yury-g/usb-buddy/docs/images/01-cable-pair.jpg

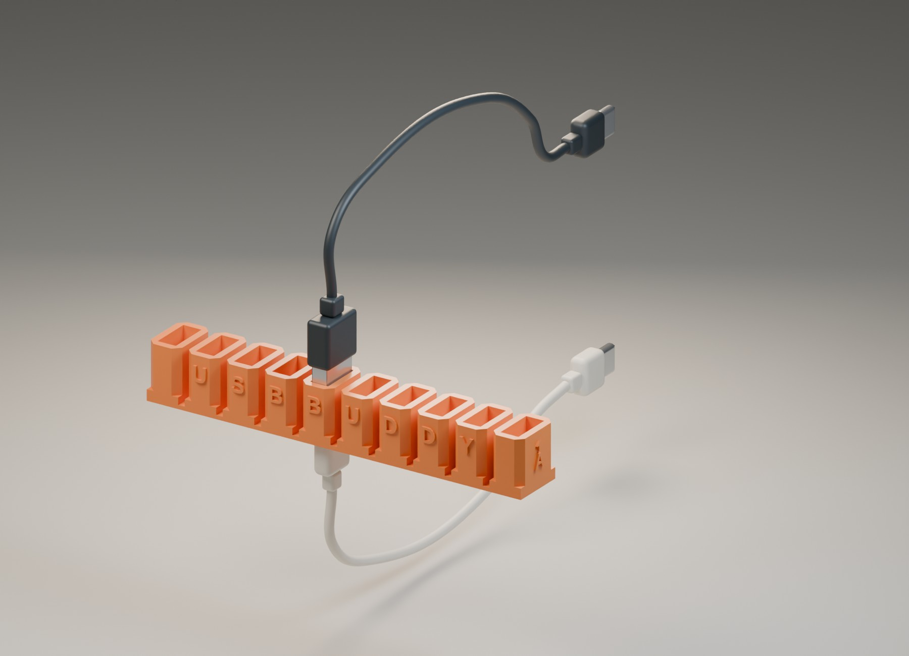
docs/images/01-cable-pair.jpg
