yury-g/usb-buddy/docs/images/drawer-before-after.jpg

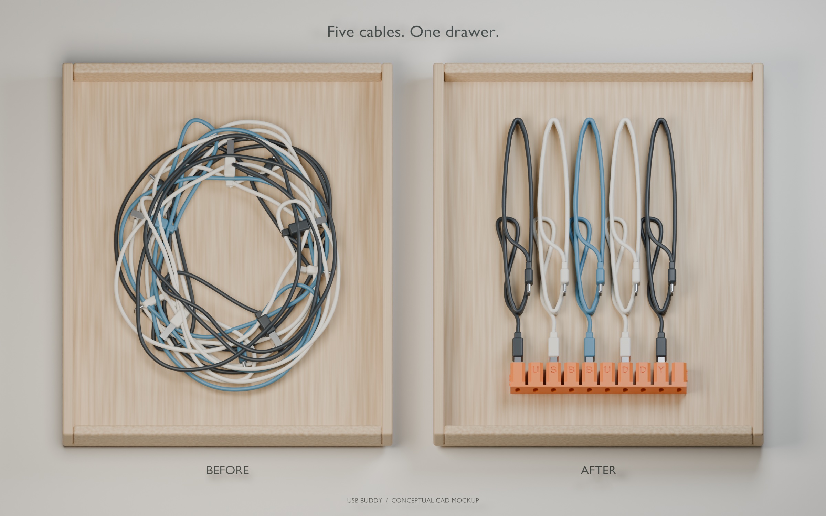
docs/images/drawer-before-after.jpg
