yury-g/usb-buddy/docs/images/drawer-clean-reference.jpg

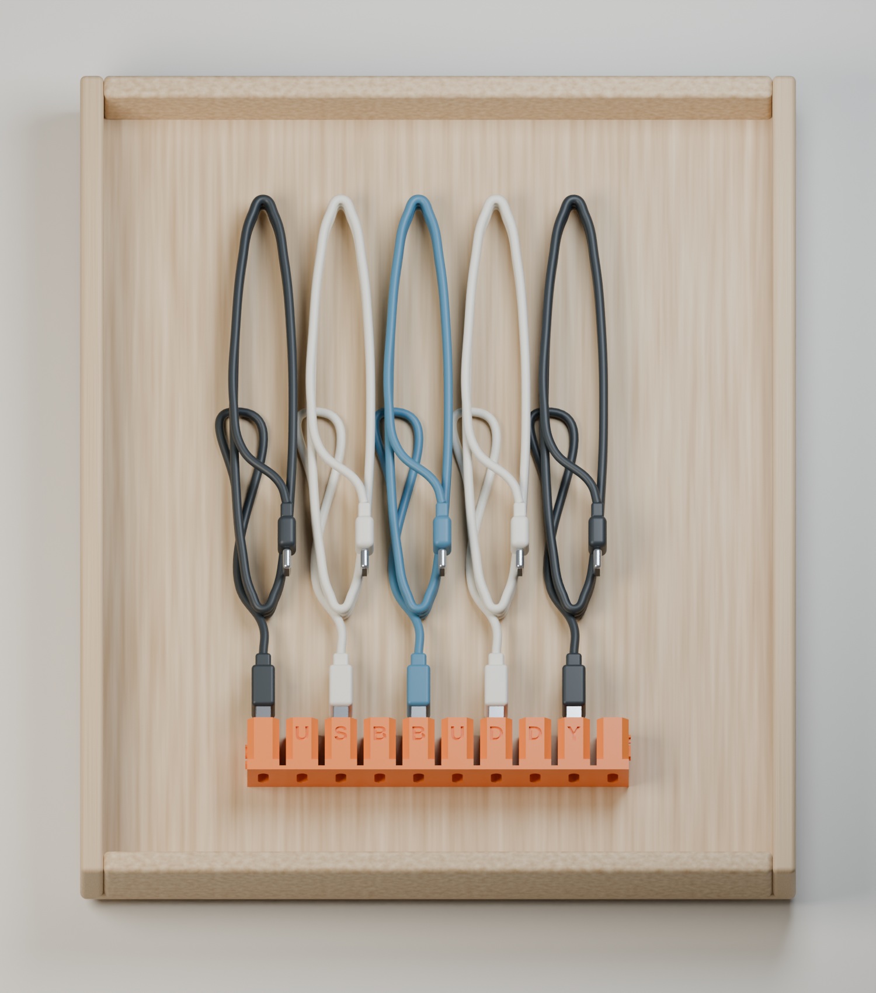
docs/images/drawer-clean-reference.jpg
