yury-g/usb-buddy/docs/images/lifestyle-evening.jpg

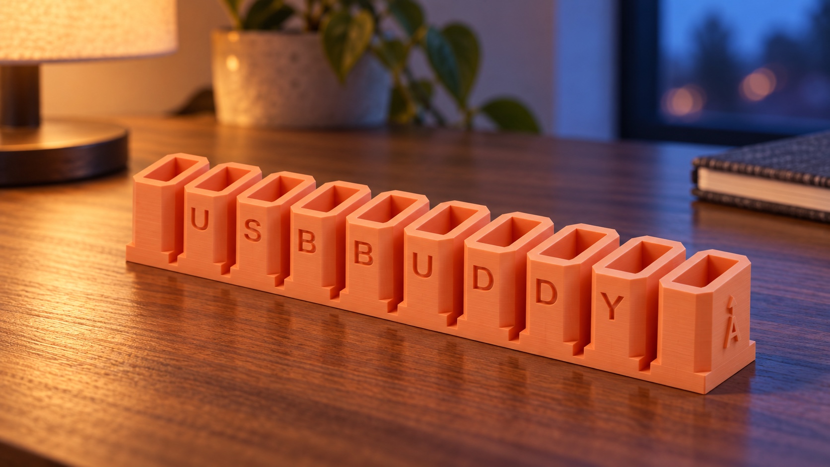
docs/images/lifestyle-evening.jpg
