yury-g/usb-buddy/docs/images/product-graphite.jpg

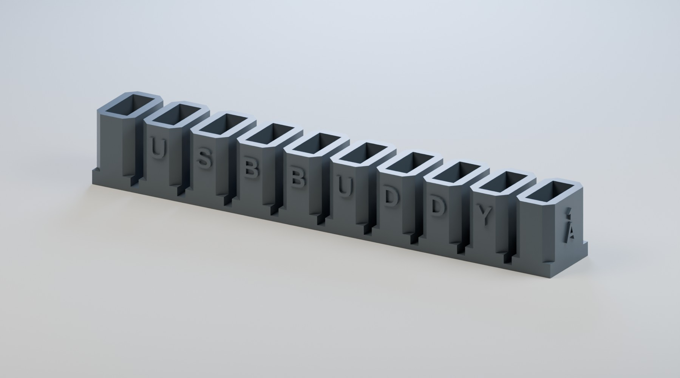
docs/images/product-graphite.jpg
